jglandorf/wspr_pi0/design_notes/lpf_04MHz.png

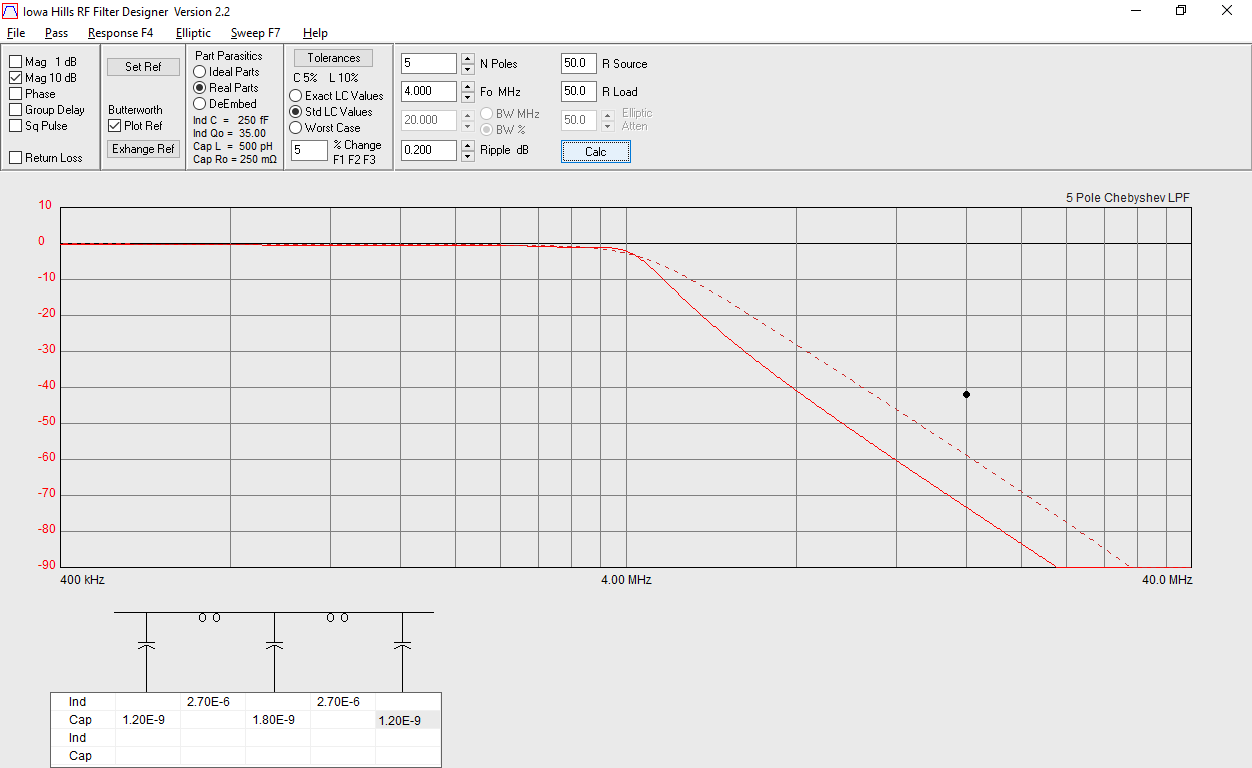
design_notes/lpf_04MHz.png
